HonzaKoren/oss_marine_datalogger/windvane/3dprint/Yacht Windvane - Backstay Inset 12-7mm.stl

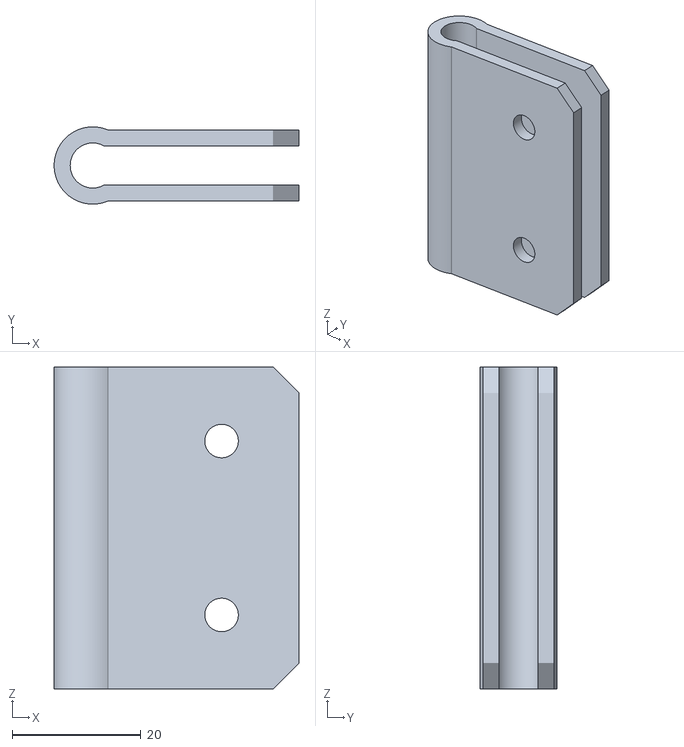
[picture p16: CAD file, 2023-07-17]
windvane/3dprint/Yacht Windvane - Backstay Inset 12-7mm.stl
38.0 x 12.0 x 50.0
