HonzaKoren/oss_marine_datalogger/windvane/3dprint/Yacht Windvane - ESP8266 socket.stl

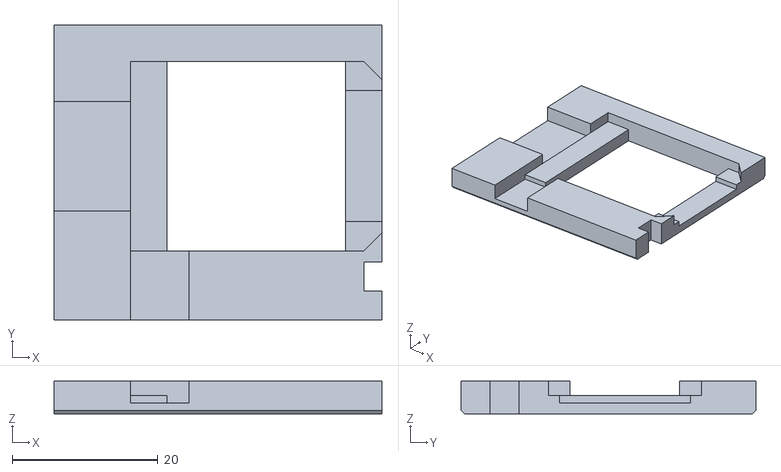
[picture p17: CAD file, 2023-05-19]
windvane/3dprint/Yacht Windvane - ESP8266 socket.stl
45.0 x 40.5 x 4.50
