HonzaKoren/oss_marine_datalogger/windvane/3dprint/Yacht Windvane - SP power controller.stl

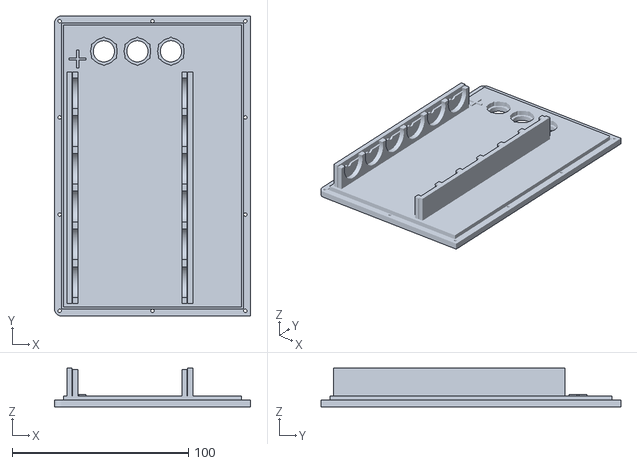
[picture p18: CAD file, 2023-05-19]
windvane/3dprint/Yacht Windvane - SP power controller.stl
111.1 x 170.0 x 22.1
