HonzaKoren/oss_marine_datalogger/windvane/3dprint/Yacht Windvane - Solar Panel Holder.stl

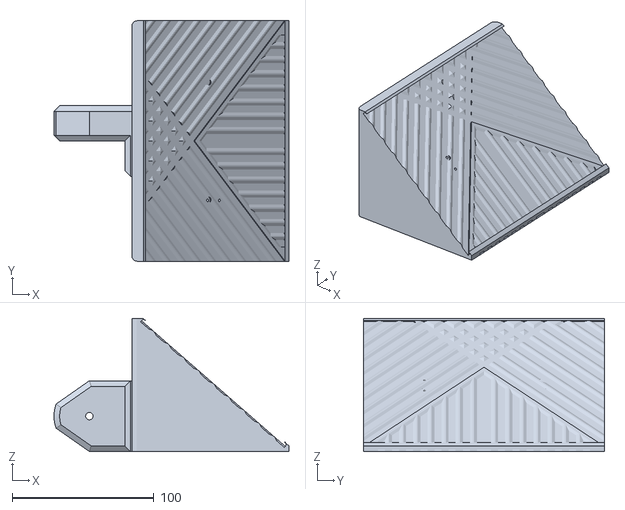
[picture p19: CAD file, 2023-05-19]
windvane/3dprint/Yacht Windvane - Solar Panel Holder.stl
166.1 x 170.0 x 94.0
