HonzaKoren/oss_marine_datalogger/windvane/3dprint/Yacht Windvane - Tilting joint.stl

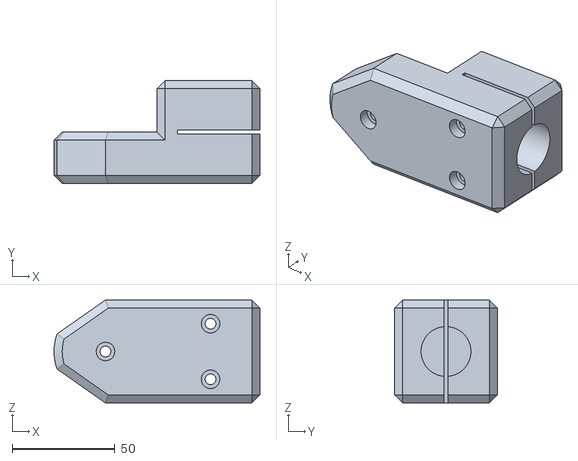
[picture p20: CAD file, 2023-05-19]
windvane/3dprint/Yacht Windvane - Tilting joint.stl
100.0 x 50.0 x 50.0
