HonzaKoren/oss_marine_datalogger/windvane/3dprint/Yacht Windvane - Power drive socket.stl

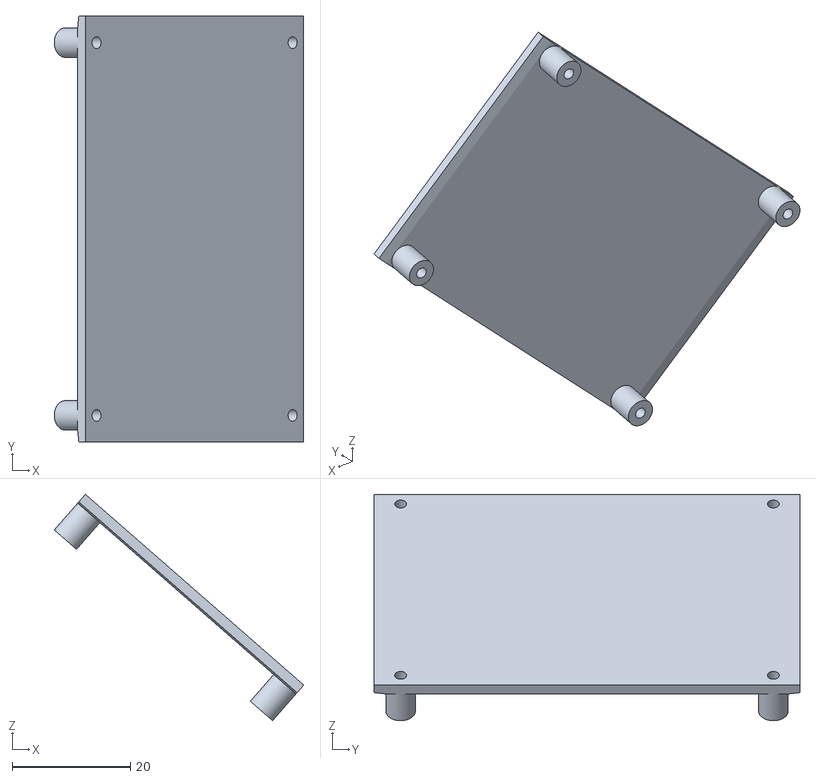
[picture p21: CAD file, 2023-05-19]
windvane/3dprint/Yacht Windvane - Power drive socket.stl
42.2 x 72.0 x 38.3
