HonzaKoren/oss_marine_datalogger/windvane/3dprint/Yacht Windvane - Windvane axis top.stl

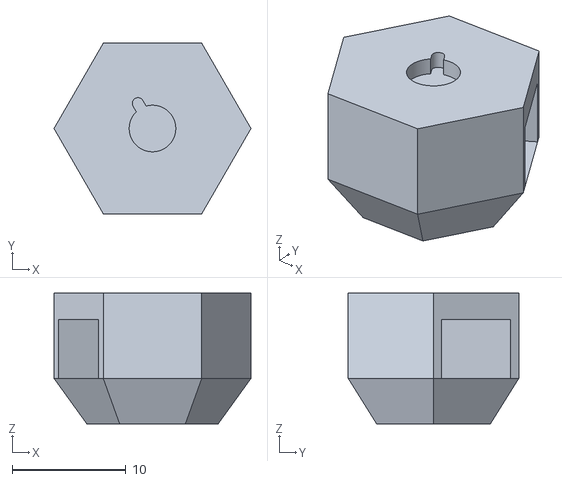
[picture p22: CAD file, 2023-05-19]
windvane/3dprint/Yacht Windvane - Windvane axis top.stl
17.3 x 15.0 x 11.5
