HonzaKoren/oss_marine_datalogger/windvane/3dprint/Yacht Windvane - Windvane axis.stl

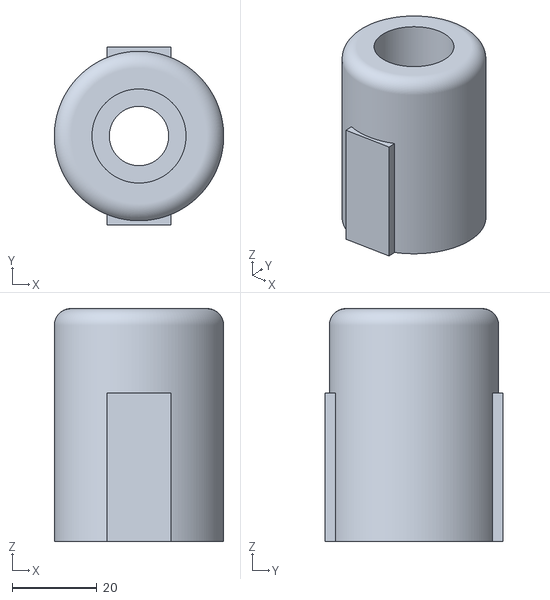
[picture p23: CAD file, 2023-05-19]
windvane/3dprint/Yacht Windvane - Windvane axis.stl
40.0 x 42.0 x 55.0
