HonzaKoren/oss_marine_datalogger/windvane/3dprint/Yacht Windvane - Axis mounting tool.stl

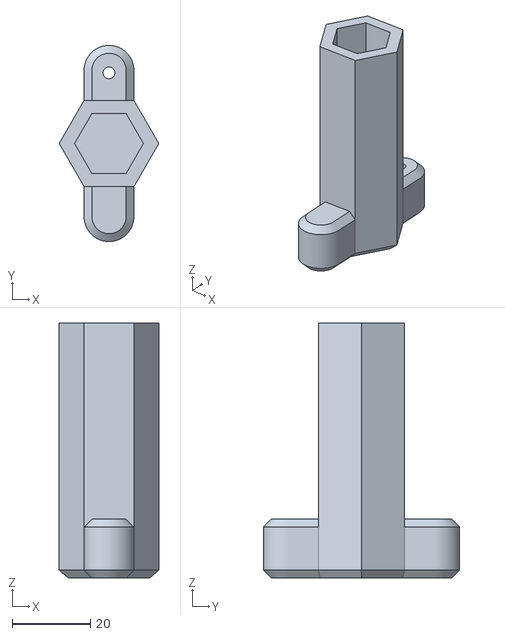
[picture p24: CAD file, 2023-05-19]
windvane/3dprint/Yacht Windvane - Axis mounting tool.stl
25.4 x 50.0 x 65.0
