HonzaKoren/oss_marine_datalogger/windvane/3dprint/Yacht Windvane - GX12 Connector Thin Cable Fixer.stl

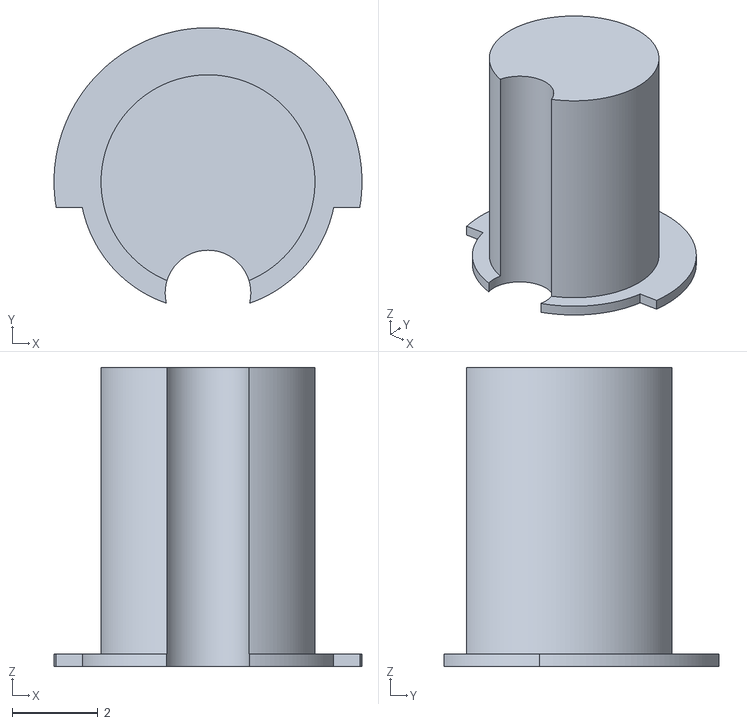
[picture p25: CAD file, 2023-05-19]
windvane/3dprint/Yacht Windvane - GX12 Connector Thin Cable Fixer.stl
7.20 x 6.44 x 7.00
