HonzaKoren/oss_marine_datalogger/windvane/3dprint/Base Station - Box.stl

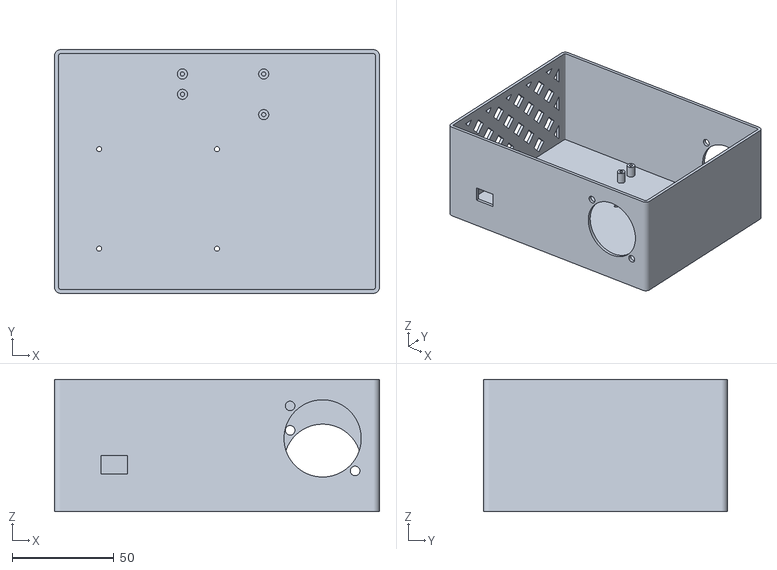
[picture p26: CAD file, 2023-05-19]
windvane/3dprint/Base Station - Box.stl
160.0 x 120.0 x 65.0
