HonzaKoren/oss_marine_datalogger/windvane/3dprint/Base Station - Lid.stl

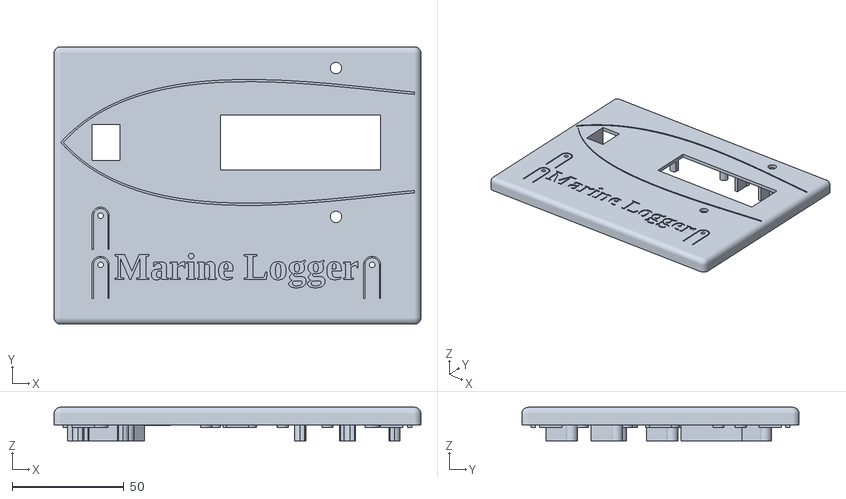
[picture p27: CAD file, 2023-05-19]
windvane/3dprint/Base Station - Lid.stl
164.0 x 124.0 x 15.0
