HonzaKoren/oss_marine_datalogger/windvane/3dprint/Yacht Windvane - GE outlet key.stl

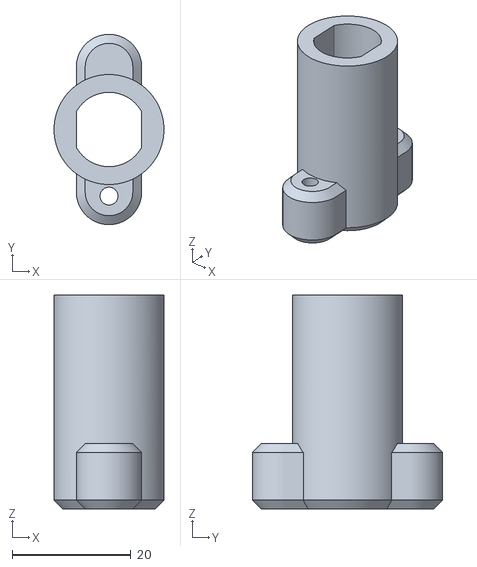
[picture p28: CAD file, 2023-05-19]
windvane/3dprint/Yacht Windvane - GE outlet key.stl
18.5 x 32.0 x 36.0
