HonzaKoren/oss_marine_datalogger/windvane/3dprint/Yacht Windvane - Tablet holder adaptor.stl

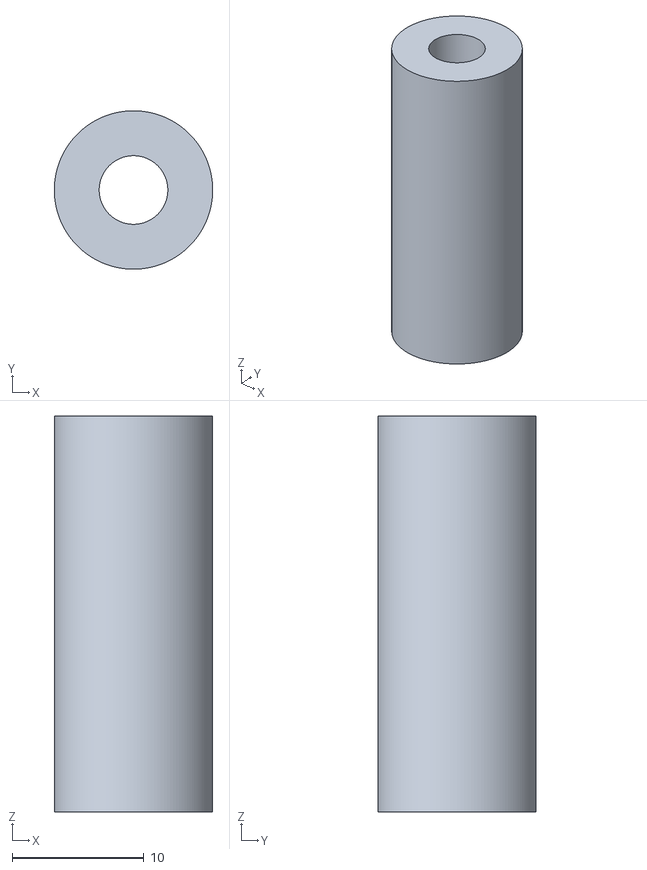
[picture p29: CAD file, 2023-05-19]
windvane/3dprint/Yacht Windvane - Tablet holder adaptor.stl
12.0 x 12.0 x 30.0
