HonzaKoren/oss_marine_datalogger/windvane/3dprint/Yacht Windvane - Joining peg.stl

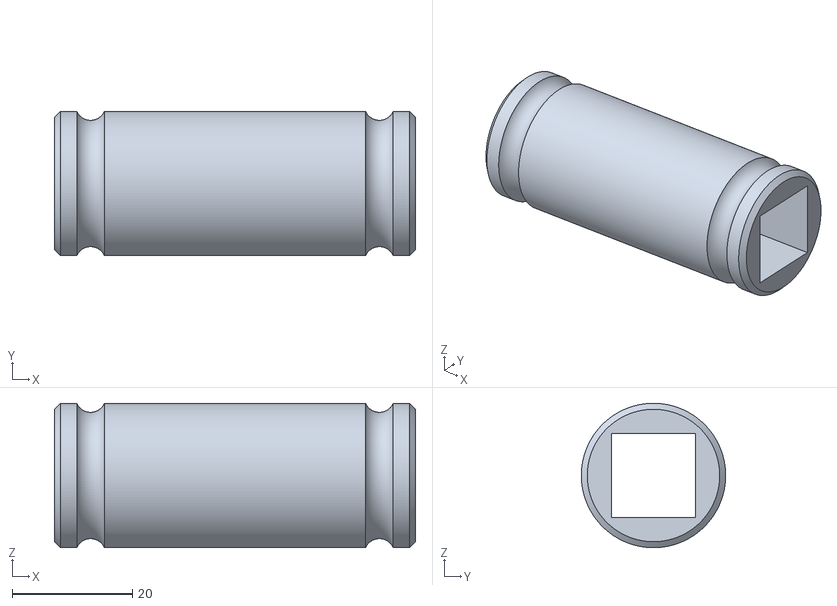
[picture p30: CAD file, 2023-05-19]
windvane/3dprint/Yacht Windvane - Joining peg.stl
60.0 x 24.0 x 24.0
