HonzaKoren/oss_marine_datalogger/windvane/3dprint/Yacht Windvane - Flap carrier.stl

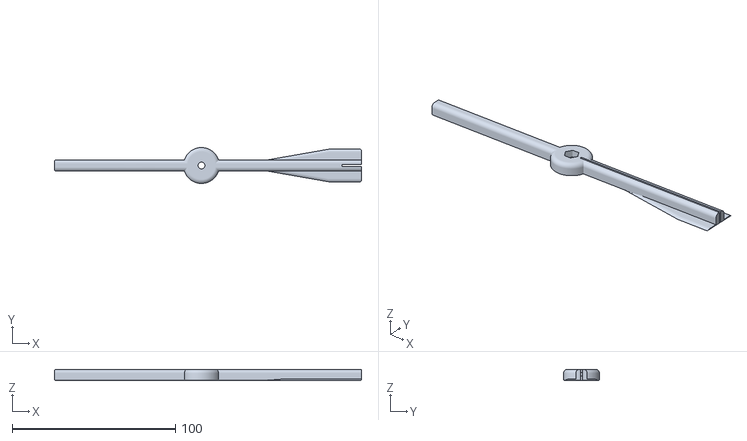
[picture p31: CAD file, 2023-05-19]
windvane/3dprint/Yacht Windvane - Flap carrier.stl
188.0 x 22.0 x 7.00
