HonzaKoren/oss_marine_datalogger/windvane/3dprint/Yacht Windvane - Peg square inside.stl

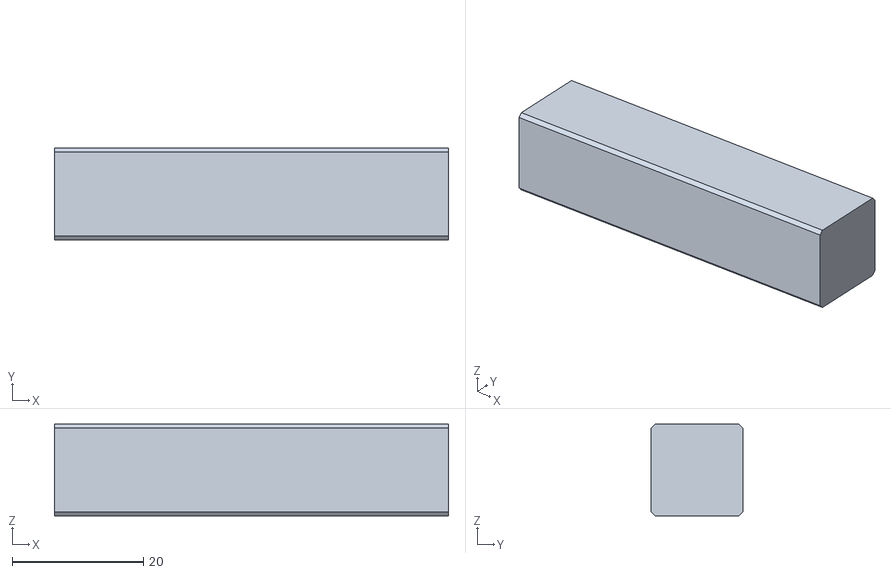
[picture p32: CAD file, 2023-05-19]
windvane/3dprint/Yacht Windvane - Peg square inside.stl
60.0 x 14.0 x 14.0
