HonzaKoren/oss_marine_datalogger/windvane/3dprint/Yacht Windvane - Flap.stl

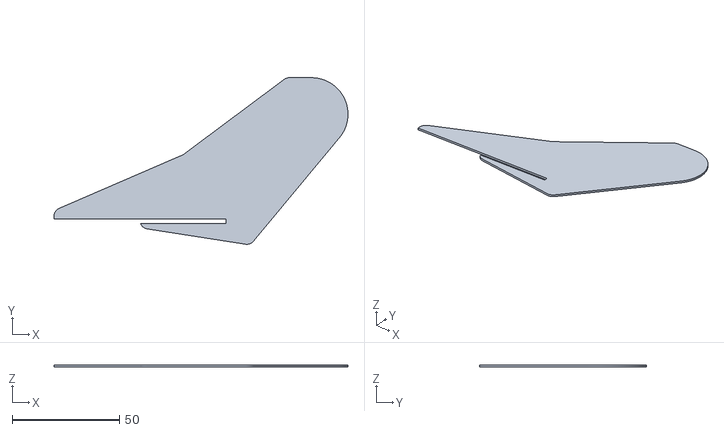
[picture p34: CAD file, 2023-05-19]
windvane/3dprint/Yacht Windvane - Flap.stl
136.8 x 77.6 x 1.00
